FreeAndFair/v4/hardware/images/v4-3dcase-2.png

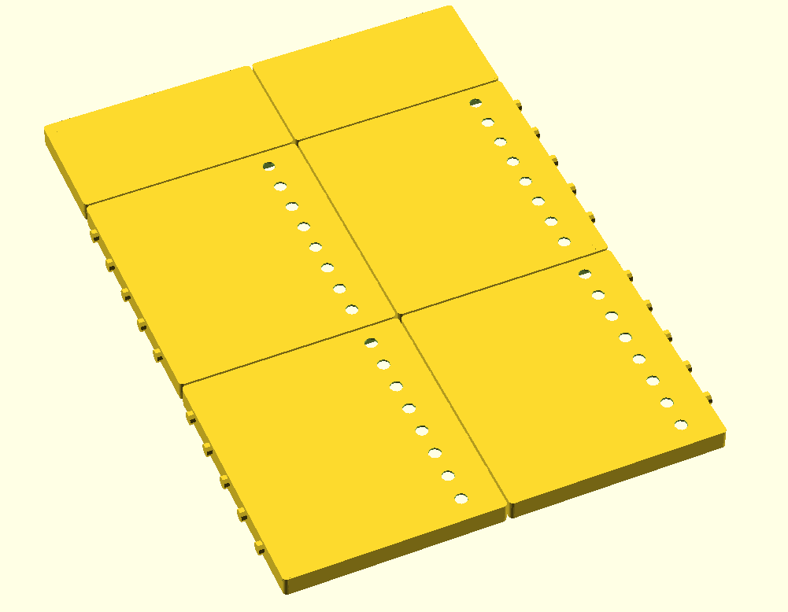
hardware/images/v4-3dcase-2.png
