FreeAndFair/v4/hardware/images/v4-atmega1284p-1-small.png

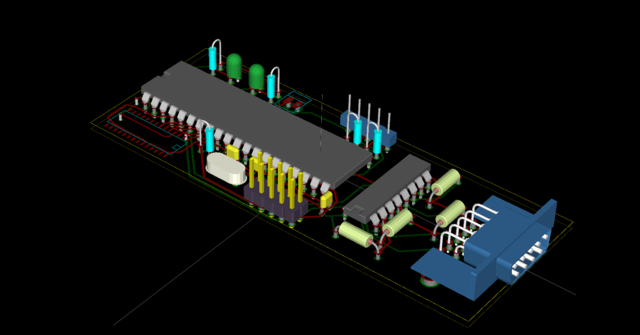
hardware/images/v4-atmega1284p-1-small.png
