FreeAndFair/v4/hardware/images/v4-atmega1284p-2.png

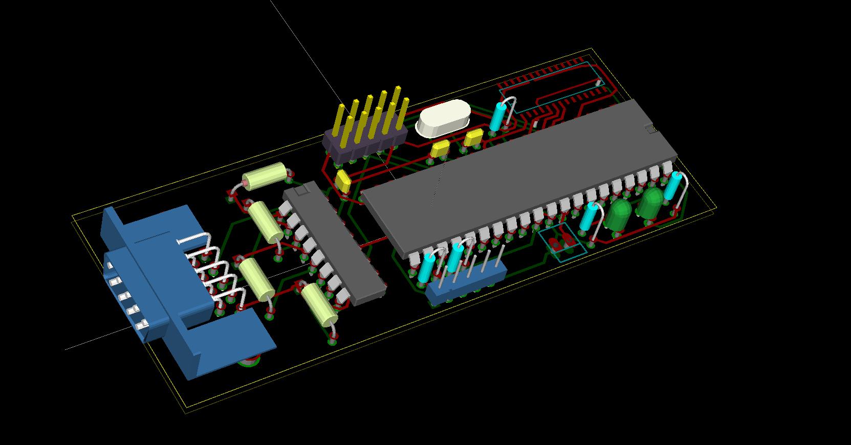
hardware/images/v4-atmega1284p-2.png
