FreeAndFair/v4/hardware/images/v4-atmega1284p.png

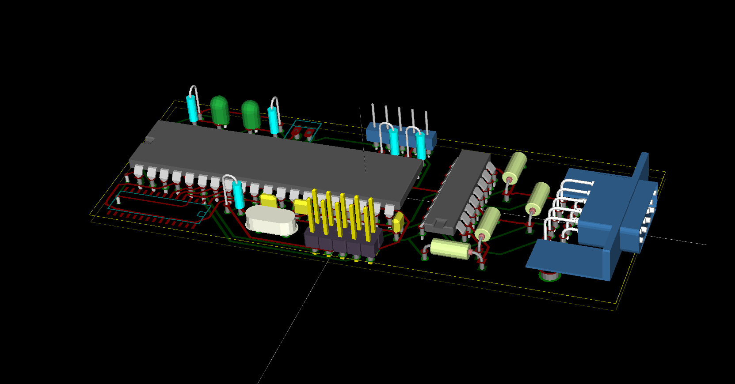
hardware/images/v4-atmega1284p.png
