FreeAndFair/v4/hardware/images/v4-crystal-and-reset.png

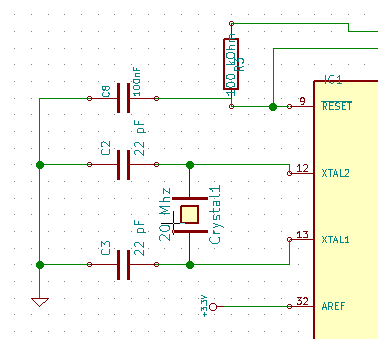
hardware/images/v4-crystal-and-reset.png
