FreeAndFair/v4/hardware/images/v4-externalflash.png

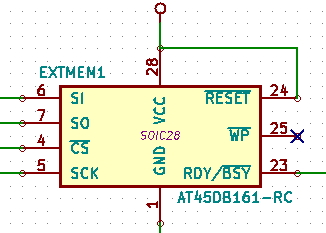
hardware/images/v4-externalflash.png
