FreeAndFair/v4/hardware/images/v4-i2c-bus.png

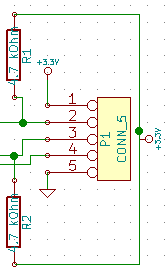
hardware/images/v4-i2c-bus.png
