FreeAndFair/v4/hardware/images/v4-i2c-expander.png

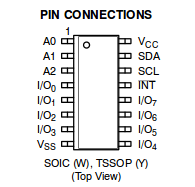
hardware/images/v4-i2c-expander.png
