FreeAndFair/v4/hardware/images/v4-uart.png

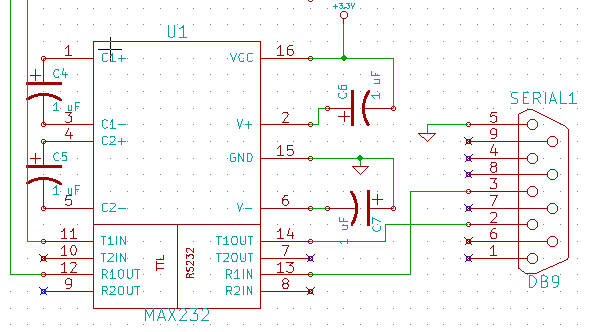
hardware/images/v4-uart.png
